RobotCing/Cing/Software/Cing Checker/img/Battery.png

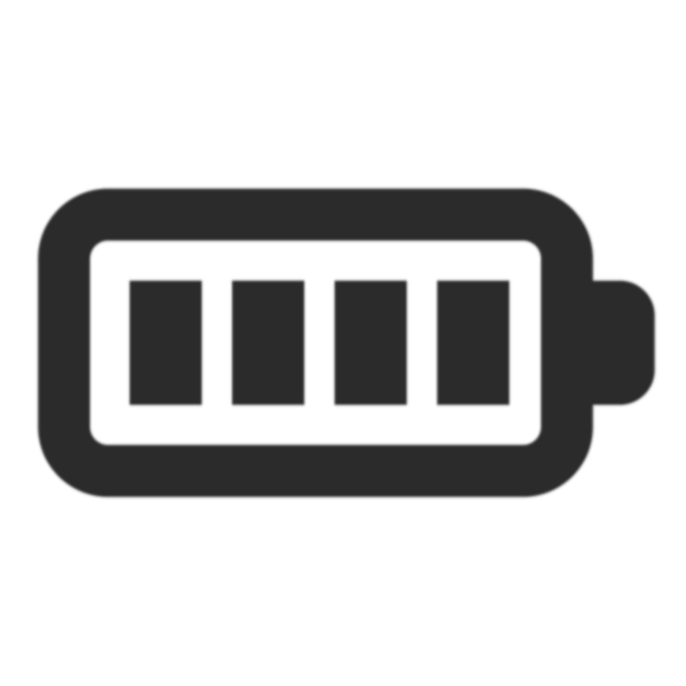
Software/Cing Checker/img/Battery.png
