RobotCing/Cing/Software/Cing Checker/img/Button.png

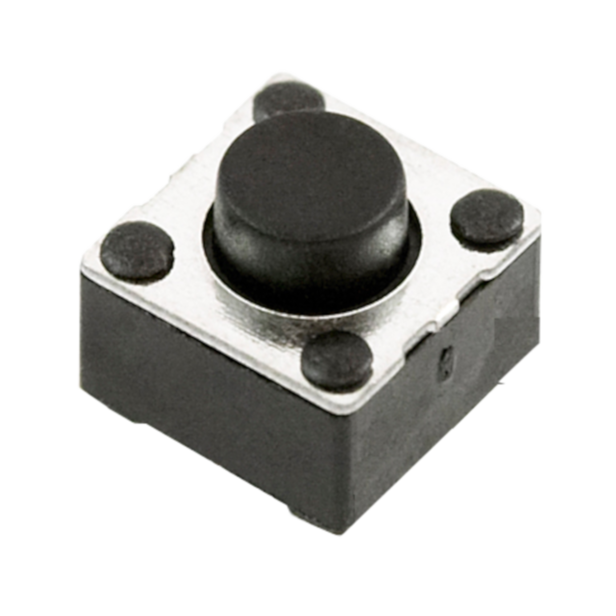
Software/Cing Checker/img/Button.png
