RobotCing/Cing/Software/Cing Checker/img/Enc.png

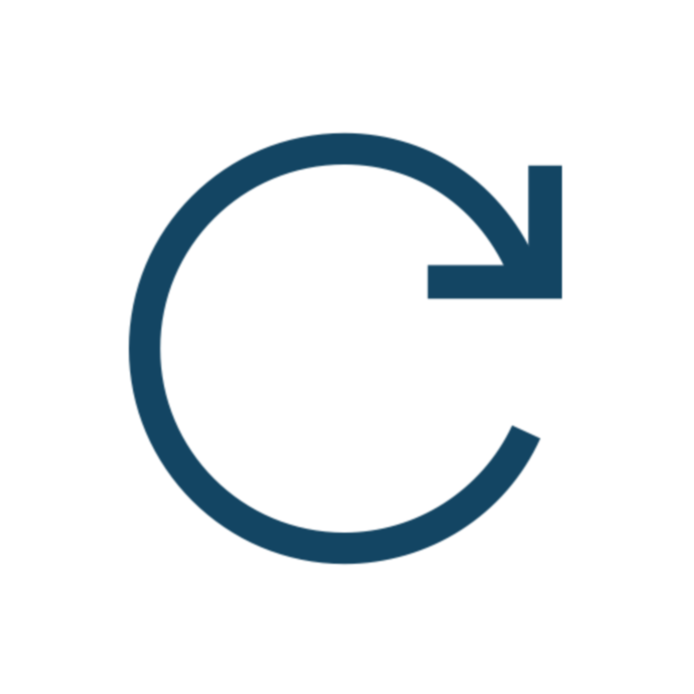
Software/Cing Checker/img/Enc.png
