RobotCing/Cing/Software/Cing Checker/img/Gyro.png

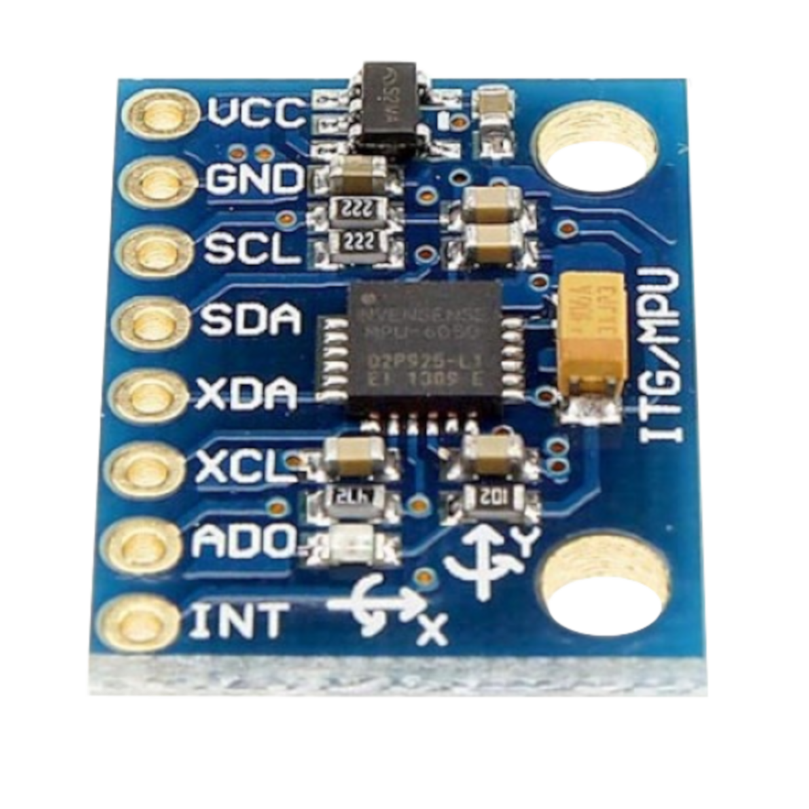
Software/Cing Checker/img/Gyro.png
