RobotCing/Cing/Software/Cing Checker/img/lidar.png

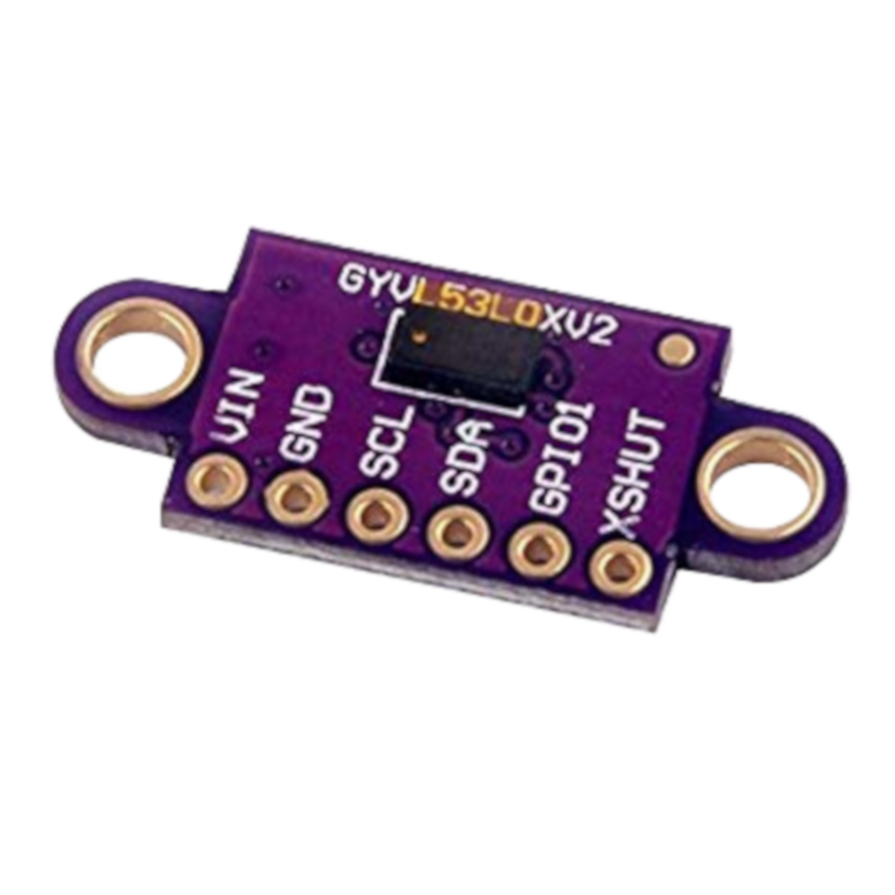
Software/Cing Checker/img/lidar.png
