RobotCing/Cing/Software/Cing Checker/img/oled.png

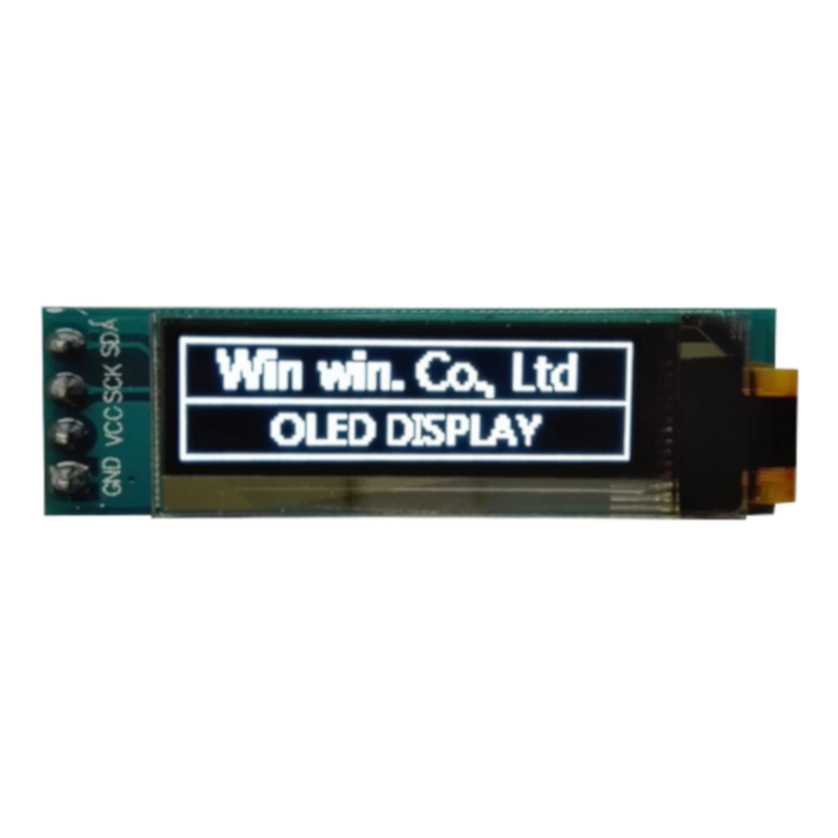
Software/Cing Checker/img/oled.png
