RobotCing/Cing/Software/Cing Checker/img/pot.png

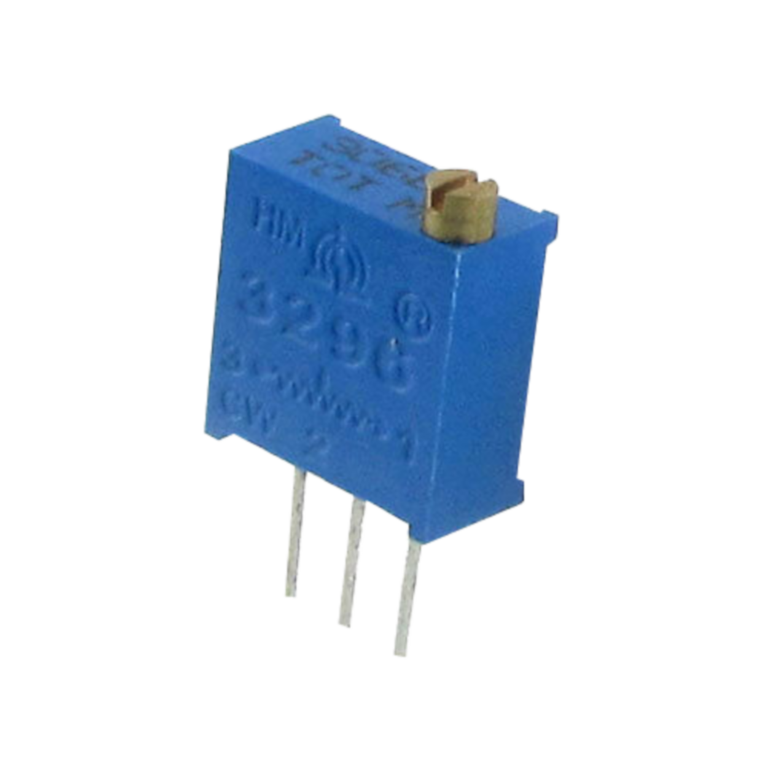
Software/Cing Checker/img/pot.png
