RobotCing/Cing/Software/Cing Checker/img/servoboard.png

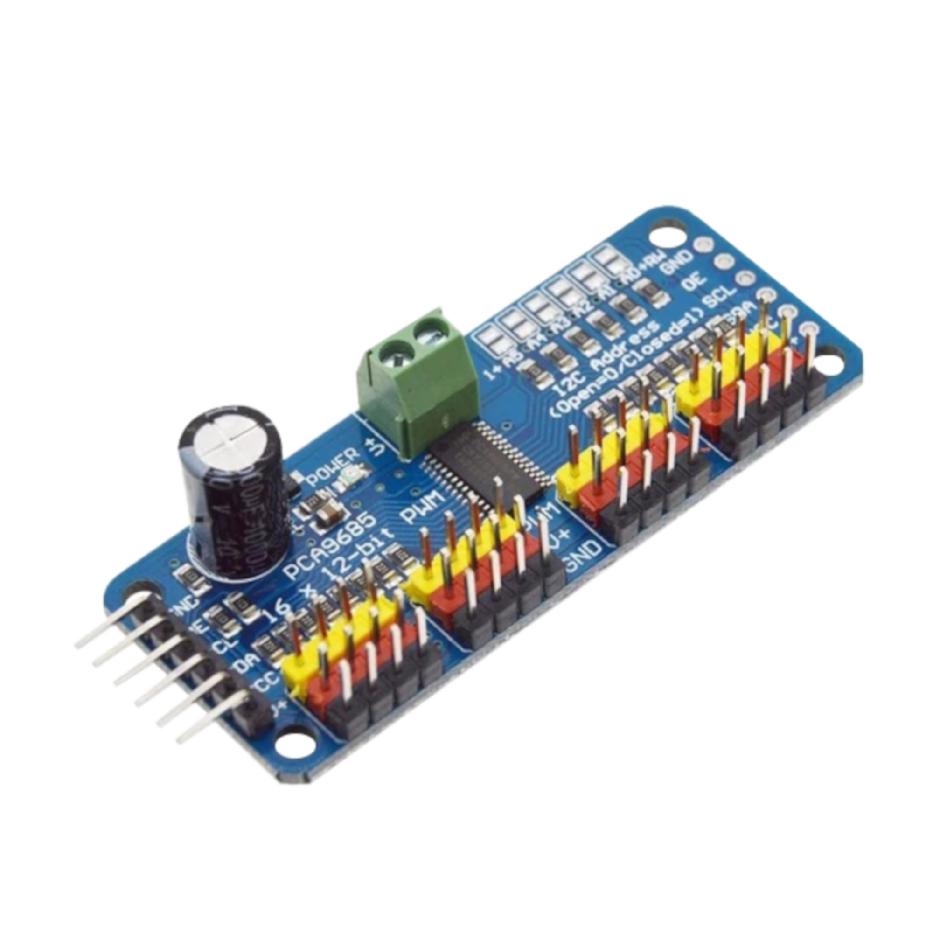
Software/Cing Checker/img/servoboard.png
