RobotCing/Cing/Software/Cing Checker/img/ultrasonic.png

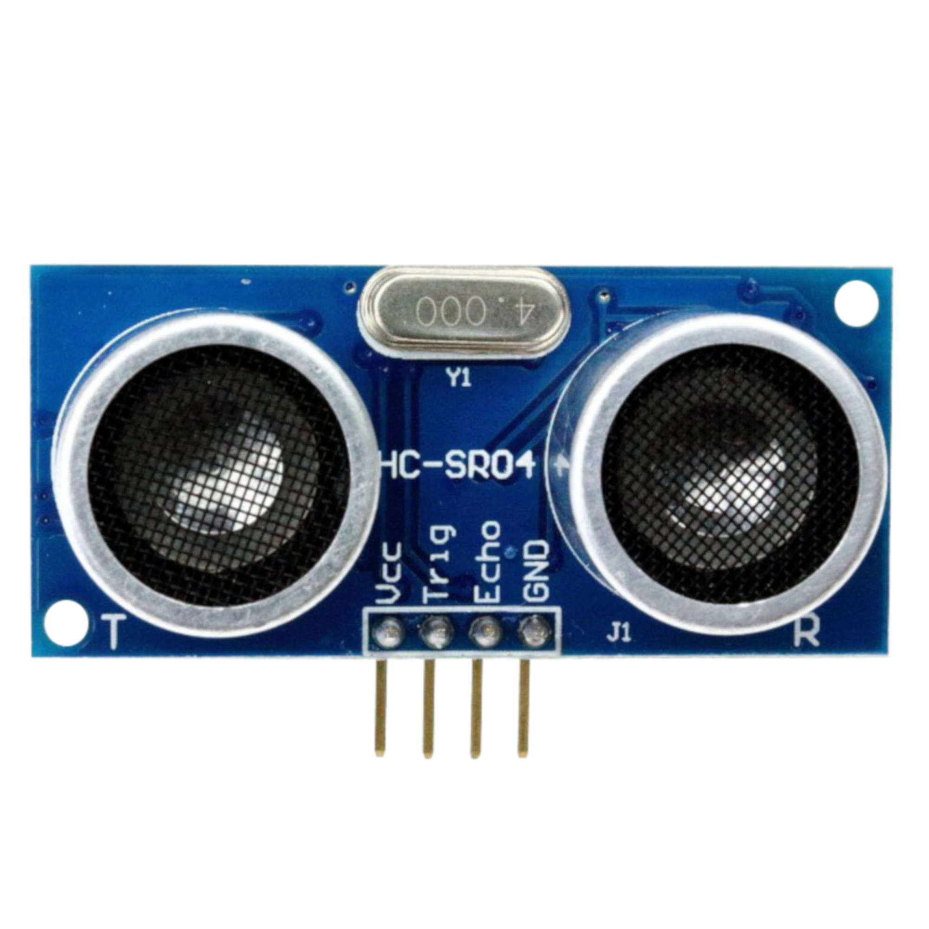
Software/Cing Checker/img/ultrasonic.png
