RobotCing/Cing/Hardware/Schematics/Procesors/Procesor-Attiny85.brd

## EAGLE design Hardware/Schematics/Procesors/Procesor-Attiny85.brd (2019-06-25)

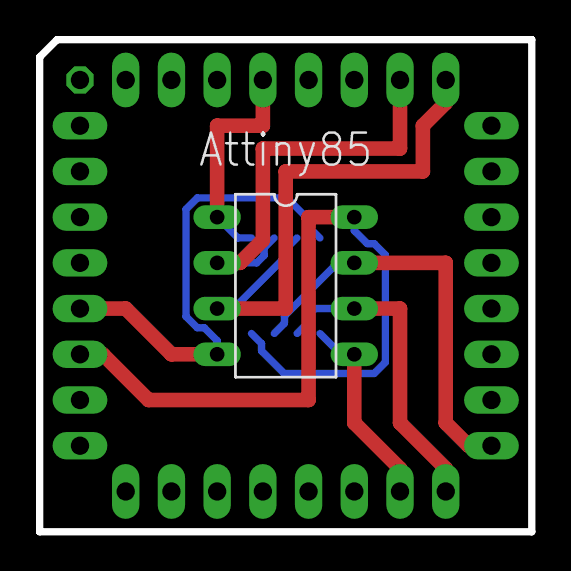
[picture p128: board Procesor-Attiny85.brd from above]

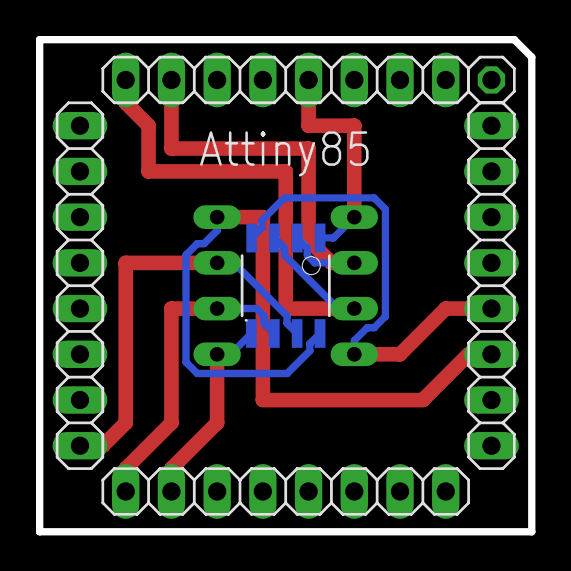
[picture p129: board Procesor-Attiny85.brd from below]

Board: 2 copper layers, 27.3 x 27.3 mm, 7 parts (6 on the bottom side), 8 nets.

Parts:
ATTINY85: DIL08
E$1: 1X01
E$2: 8S1
E$9, E$10, E$11, E$12: 1X08

Connections:
S$2: ATTINY85.1, E$2.1, E$10.5
S$3: ATTINY85.4, E$2.4, E$9.4
S$4: ATTINY85.8, E$2.8, E$9.3
S$5: ATTINY85.7, E$2.7, E$11.8
S$6: ATTINY85.3, E$2.3, E$10.1
S$7: ATTINY85.2, E$2.2, E$10.2
S$8: ATTINY85.5, E$2.5, E$12.7
S$10: ATTINY85.6, E$2.6, E$12.8
