RobotCing/Cing/Hardware/Schematics/Procesors/Procesor-Attiny84.brd

## EAGLE design Hardware/Schematics/Procesors/Procesor-Attiny84.brd (2019-08-14)

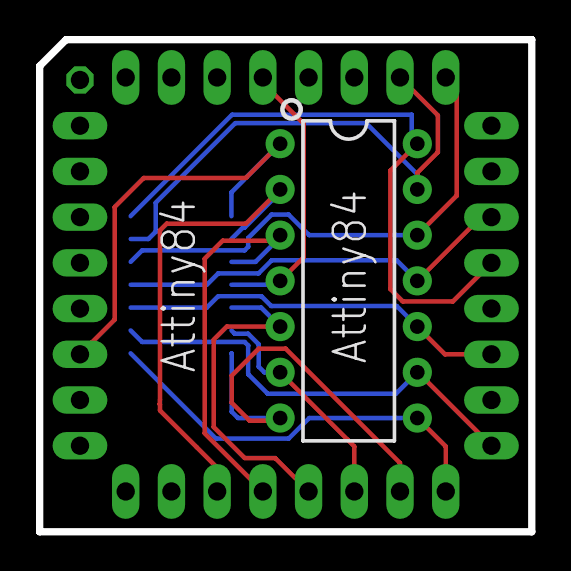
[picture p130: board Procesor-Attiny84.brd from above]

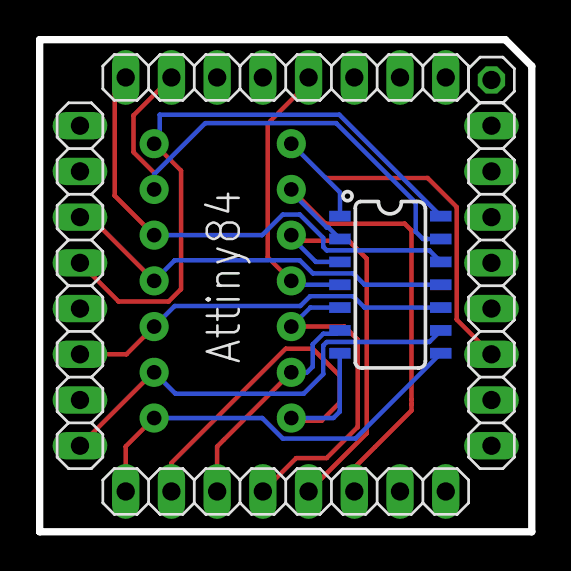
[picture p131: board Procesor-Attiny84.brd from below]

Board: 2 copper layers, 27.3 x 27.3 mm, 7 parts (6 on the bottom side), 14 nets.

Parts:
E$1: DIP14
E$2: 1X01
E$3: SO14
E$9, E$10, E$11, E$12: 1X08

Connections:
S$2: E$1.4, E$3.4, E$10.5
S$3: E$1.14, E$3.14, E$11.4
S$4: E$1.1, E$3.1, E$9.3
S$5: E$1.9, E$3.9, E$11.8
S$6: E$1.12, E$3.12, E$10.1
S$7: E$1.13, E$3.13, E$10.2
S$8: E$1.7, E$3.7, E$12.7
S$10: E$1.8, E$3.8, E$12.8
S$11: E$1.10, E$3.10, E$11.6
S$12: E$1.11, E$3.11, E$11.3
S$13: E$1.2, E$3.2, E$12.3
S$14: E$1.3, E$3.3, E$12.4
S$15: E$1.5, E$3.5, E$12.5
S$18: E$1.6, E$3.6, E$12.6
