RobotCing/Cing/Programy/00_Osvetlenie.ino

#include "Attiny84_IO_basic.h"
Attiny attiny;
#dafine ciara 0
void setup() {}
void loop() 
{
if (attiny.ShineSensor()<20)
   {
    attiny.motor("AB", 0, "digital");
   }
else 
   {
    if (attiny.LightSensor(2, "digital")==ciara) 
      {
        attiny.motor("B", 1, "digital");
      }
    else 
      {
        attiny.motor("A", 1, "digital");
      } 
   }
}
