RobotCing/Cing/Attiny85_IO_basic/Attiny85_IO_basic.h

#ifndef Attiny85_IO_basic
#define Attiny85_IO_basic
#include "Arduino.h"

class Attiny
{
  public:
    //constructor
    Attiny();
    void motor(String motor,int speed= 100,String mode = "digital");
    int LightSensor(int sensor = 1,String mode = "digital");
    
  private:
      
};
#endif
